ArrowElectronics/10BASE-T1L-MC/Wiki_Page_Images/PCBA_BackView.JPG

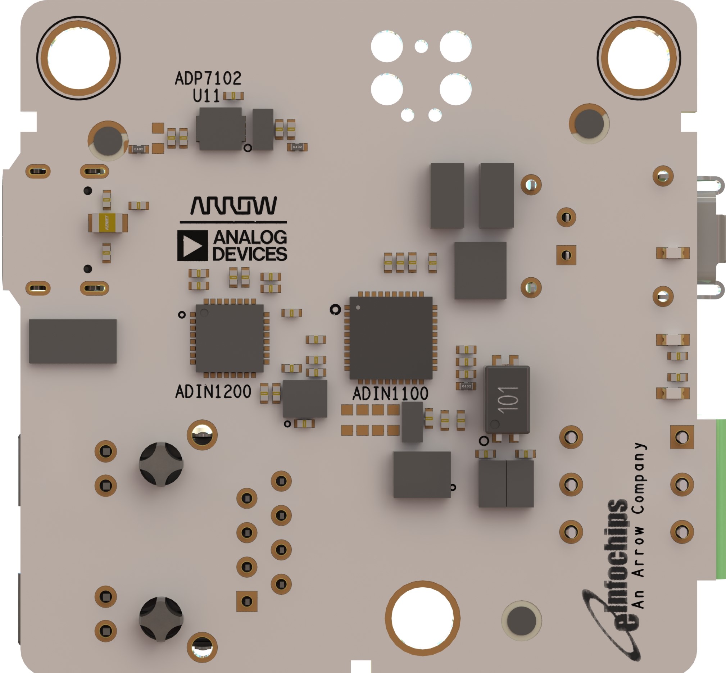
Wiki_Page_Images/PCBA_BackView.JPG
