ArrowElectronics/10BASE-T1L-MC/HW_Package/Gerber/FAB.pdf

D

1

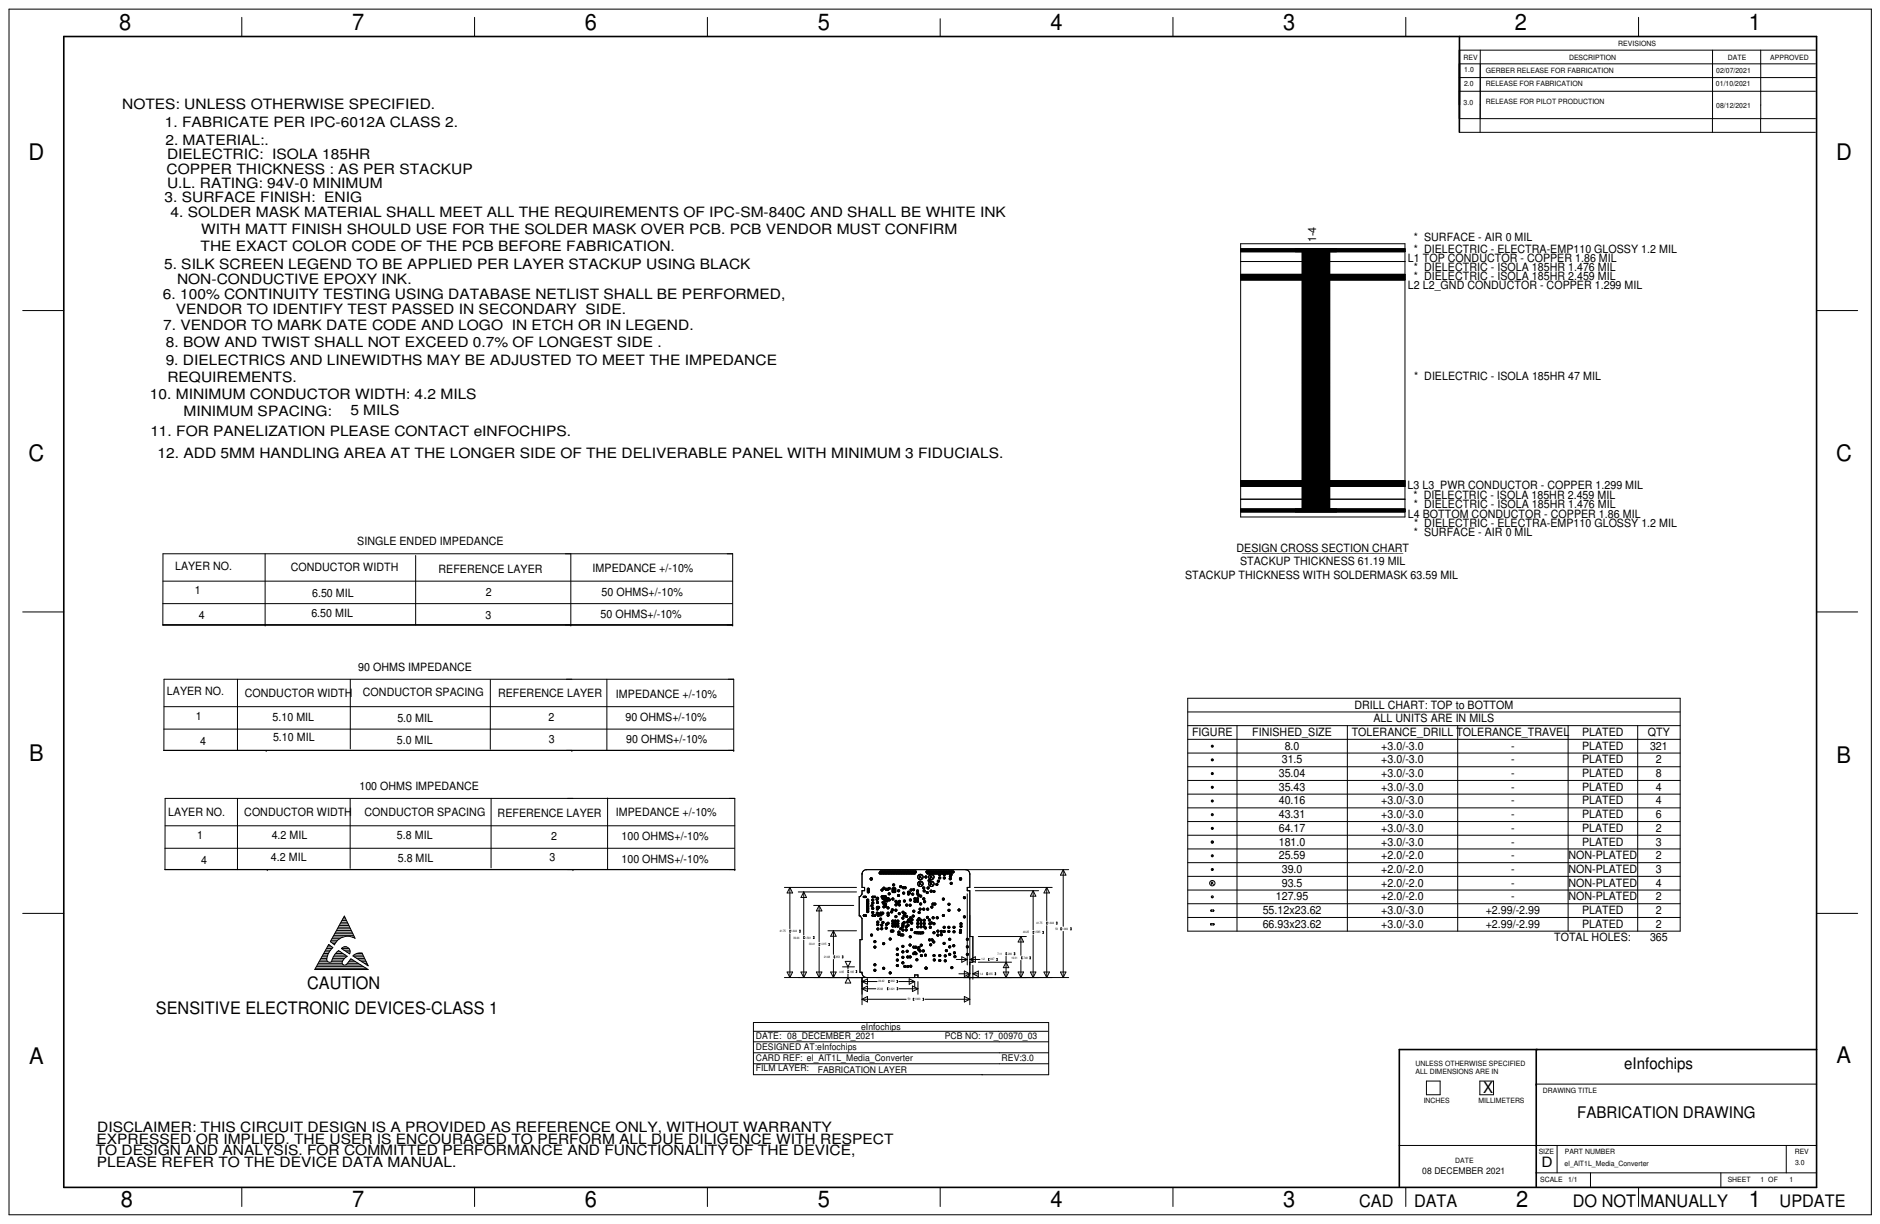
[picture p42: page 1]
REV:3.0; eInfochips; FABRICATION LAYER; PCB NO:; 5.0 MIL; 5.8 MIL; 5.10 MIL; 90 OHMS+/-10%; LAYER NO.; CONDUCTOR WIDTH; 4.2 MIL; el_AlT1L_Media_Converter; REFERENCE LAYER; IMPEDANCE +/-10%; 100 OHMS+/-10%; 90 OHMS IMPEDANCE; 100 OHMS IMPEDANCE; CONDUCTOR SPACING; 08_DECEMBER_2021; PLATED; QTY; FIGURE; TOLERANCE_DRILL FINISHED_SIZE; TOLERANCE_TRAVEL; TOTAL HOLES:; NON-PLATED; CAUTION; MINIMUM SPACING:; 5 MILS; DRAWING TITLE; MILLIMETERS; INCHES; FABRICATION DRAWING; UPDATE; DO NOT MANUALLY; CAD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

REVISIONS

REV | DESCRIPTION | DATE | APPROVED
1.0 | GERBER RELEASE FOR FABRICATION | 02/07/2021

2.0 | RELEASE FOR FABRICATION | 01/10/2021

NOTES: UNLESS OTHERWISE SPECIFIED.

3.0 | | 08/12/2021 RELEASE FOR PILOT PRODUCTION

1. FABRICATE PER IPC-6012A CLASS 2.
2. MATERIAL:.
DIELECTRIC: ISOLA 185HR
COPPER THICKNESS : AS PER STACKUP
U.L. RATING: 94V-0 MINIMUM
3. SURFACE FINISH: ENIG
4. SOLDER MASK MATERIAL SHALL MEET ALL THE REQUIREMENTS OF IPC-SM-840C AND SHALL BE WHITE INK
WITH MATT FINISH SHOULD USE FOR THE SOLDER MASK OVER PCB. PCB VENDOR MUST CONFIRM
THE EXACT COLOR CODE OF THE PCB BEFORE FABRICATION.
5. SILK SCREEN LEGEND TO BE APPLIED PER LAYER STACKUP USING BLACK
NON-CONDUCTIVE EPOXY INK.
6. 100% CONTINUITY TESTING USING DATABASE NETLIST SHALL BE PERFORMED,
VENDOR TO IDENTIFY TEST PASSED IN SECONDARY SIDE.
7. VENDOR TO MARK DATE CODE AND LOGO IN ETCH OR IN LEGEND.
8. BOW AND TWIST SHALL NOT EXCEED 0.7% OF LONGEST SIDE .
9. DIELECTRICS AND LINEWIDTHS MAY BE ADJUSTED TO MEET THE IMPEDANCE
REQUIREMENTS.
10. MINIMUM CONDUCTOR WIDTH: 4.2 MILS
11. FOR PANELIZATION PLEASE CONTACT eINFOCHIPS.
12. ADD 5MM HANDLING AREA AT THE LONGER SIDE OF THE DELIVERABLE PANEL WITH MINIMUM 3 FIDUCIALS.

* SURFACE - AIR 0 MIL
* DIELECTRIC - ELECTRA-EMP110 GLOSSY 1.2 MIL
L1 TOP CONDUCTOR - COPPER 1.86 MIL
* DIELECTRIC - ISOLA 185HR 1.476 MIL
* DIELECTRIC - ISOLA 185HR 2.459 MIL
L2 L2_GND CONDUCTOR - COPPER 1.299 MIL

* DIELECTRIC - ISOLA 185HR 47 MIL

L3 L3_PWR CONDUCTOR - COPPER 1.299 MIL * DIELECTRIC - ISOLA 185HR 2.459 MIL
L4 BOTTOM CONDUCTOR - COPPER 1.86 MIL

SINGLE ENDED IMPEDANCE

DESIGN CROSS SECTION CHART ___________________________ STACKUP THICKNESS 61.19 MIL

LAYER NO. | CONDUCTOR WIDTH | REFERENCE LAYER | IMPEDANCE +/-10%

STACKUP THICKNESS WITH SOLDERMASK 63.59 MIL

1 | 6.50 MIL | 2 | 50 OHMS+/-10%

4 | 6.50 MIL | 3 | 50 OHMS+/-10%

LAYER NO. | CONDUCTOR WIDTH | CONDUCTOR SPACING | REFERENCE LAYER | IMPEDANCE +/-10%

1 | 5.10 MIL | 5.0 MIL | 2 | 90 OHMS+/-10%

DRILL CHART: TOP to BOTTOM
ALL UNITS ARE IN MILS

35.04 | +3.0/-3.0 | - | PLATED | 8
35.43 | +3.0/-3.0 | - | PLATED | 4

39.0 | +2.0/-2.0 | - | NON-PLATED | 3
93.5 | +2.0/-2.0 | - | NON-PLATED | 4
127.95 | +2.0/-2.0 | - | NON-PLATED | 2
55.12x23.62 | +3.0/-3.0 | +2.99/-2.99 | PLATED | 2
66.93x23.62 | +3.0/-3.0 | +2.99/-2.99 | PLATED | 2

SENSITIVE ELECTRONIC DEVICES-CLASS 1

DATE:
DESIGNED AT:eInfochips
CARD REF:
FILM LAYER:

UNLESS OTHERWISE SPECIFIED
ALL DIMENSIONS ARE IN

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

DATE 08 DECEMBER 2021 | SIZE D | PART NUMBER el_AlT1L_Media_Converter | REV 3.0

SCALE 1/1 | | SHEET 1 OF 1
