ArrowElectronics/10BASE-T1L-MC/HW_Package/Block Diagram/ADI_Media_Converter_Block_Diagram_Beta.pdf

# 10BASE-T1L Media Converter Dongle Hardware Architecture

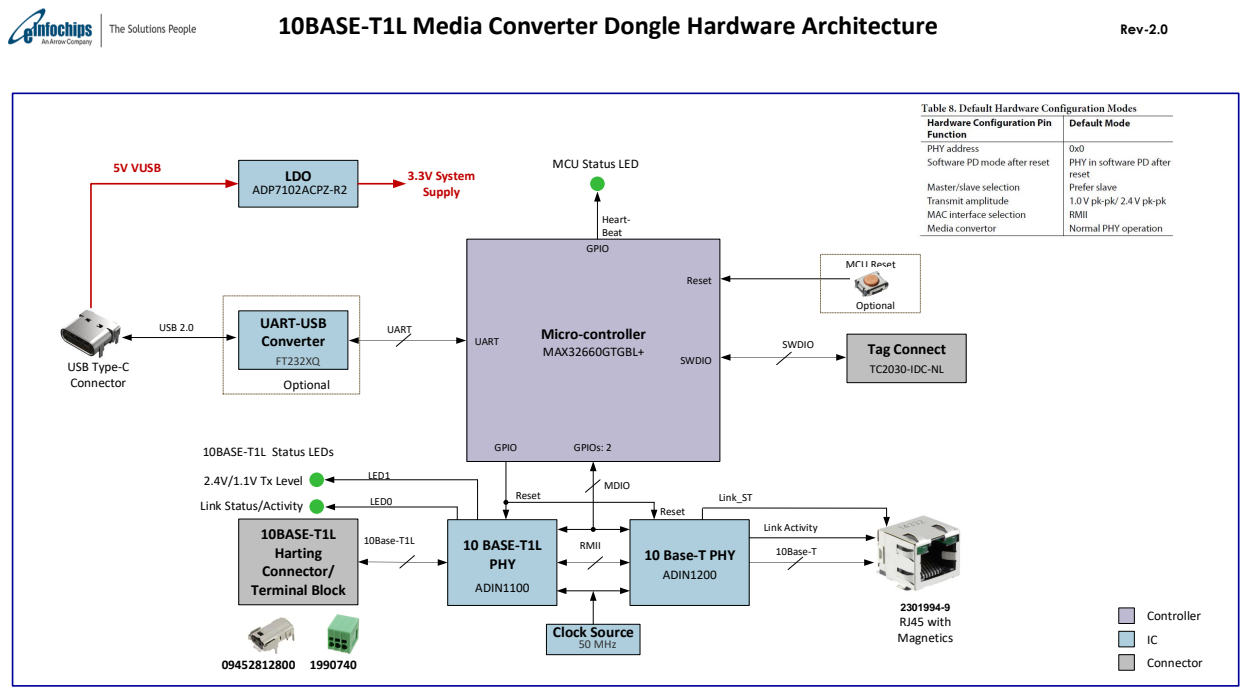
[picture p43: page 1]
10 Base-T PHY; ADIN1200; 10 BASE-T1L PHY; ADIN1100; Micro-controller MAX32660GTGBL+; 2301994-9 RJ45 with Magnetics; 10Base-T; 10BASE-T1L Harting Connector/ Terminal Block; MDIO; 10Base-T1L; RMII; Reset; Clock Source 50 MHz; Rev-2.0; Link_ST; UART; GPIO; GPIOs: 2; Heart- Beat; Link Activity; 10BASE-T1L Status LEDs; Controller; Connector; SWDIO; UART-USB Converter; Optional; USB 2.0; MCU Reset; USB Type-C Connector; LDO ADP7102ACPZ-R2; 3.3V System Supply; 5V VUSB; Tag Connect; TC2030-IDC-NL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

MCU Status LED

2.4V/1.1V Tx Level
Link Status/Activity

# Revision History

Version | Date | Description
0.1 | 1-May-21 | Initial Draft
0.2 | 3-May-21 | Placement Feasibility added
0.3 | 7-May-21 | DC Jack removed
0.4 | 13-May-21 | EEPROM removed; INT and Reset are changed to optional
0.5 | 20-May-21 | Power LED and T1L Link Status LED is removed
0.6 | 28-May-21 | LED1 is added on ADIN1100
0.7 | 02-Jun-21 | Link Status signals to MCU and INT are deleted.
1.0 | 02-Jul-21 | Baselined
1.1 | 2-Sep-21 | RJ45 part# changed to 2301994-9 Buck regulator part# changed to LDO ADP7102ACPZ-R2
2.0 | 07-Oct-21 | Baselined
