ArrowElectronics/10BASE-T1L-MC/HW_Package/Gerber/LAYERS.pdf

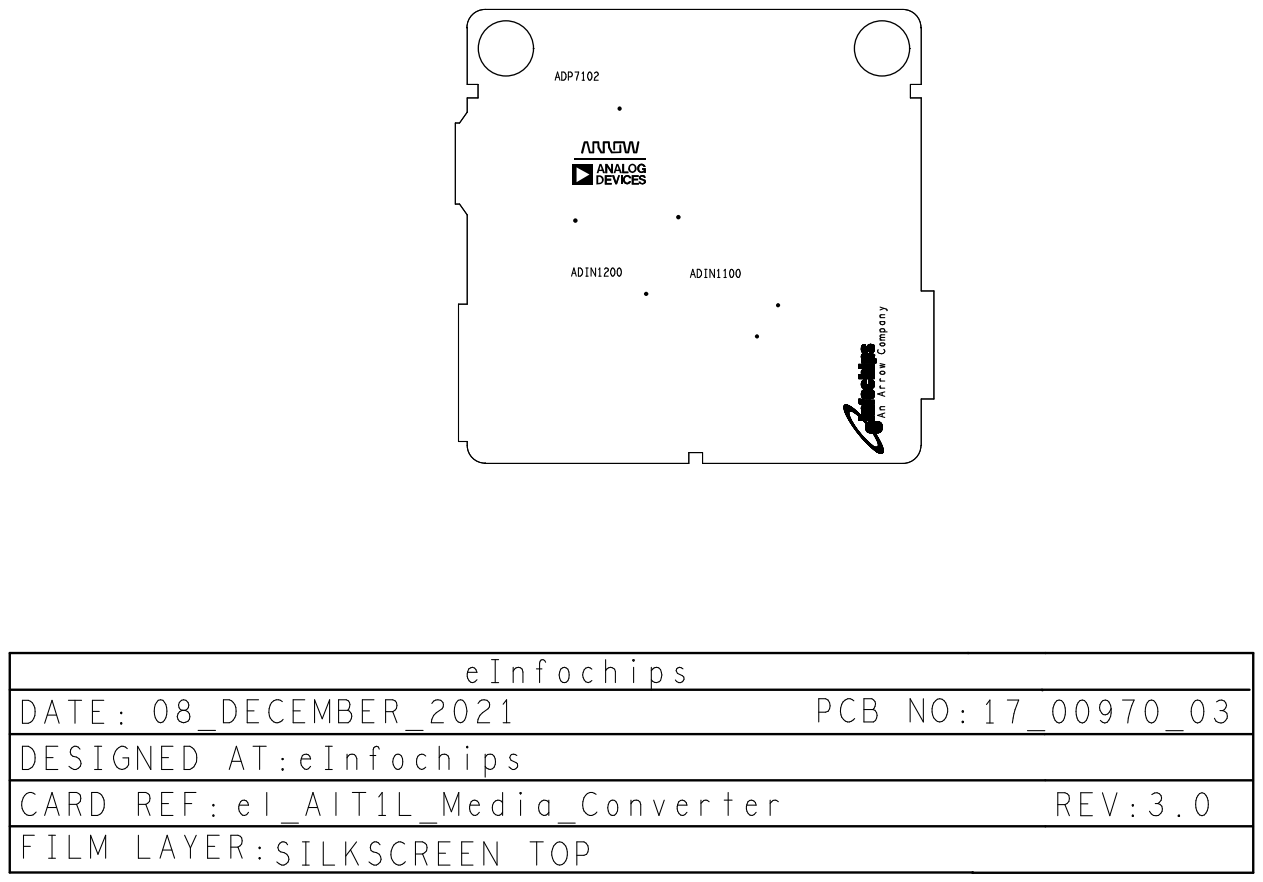
[picture p51: page 1]


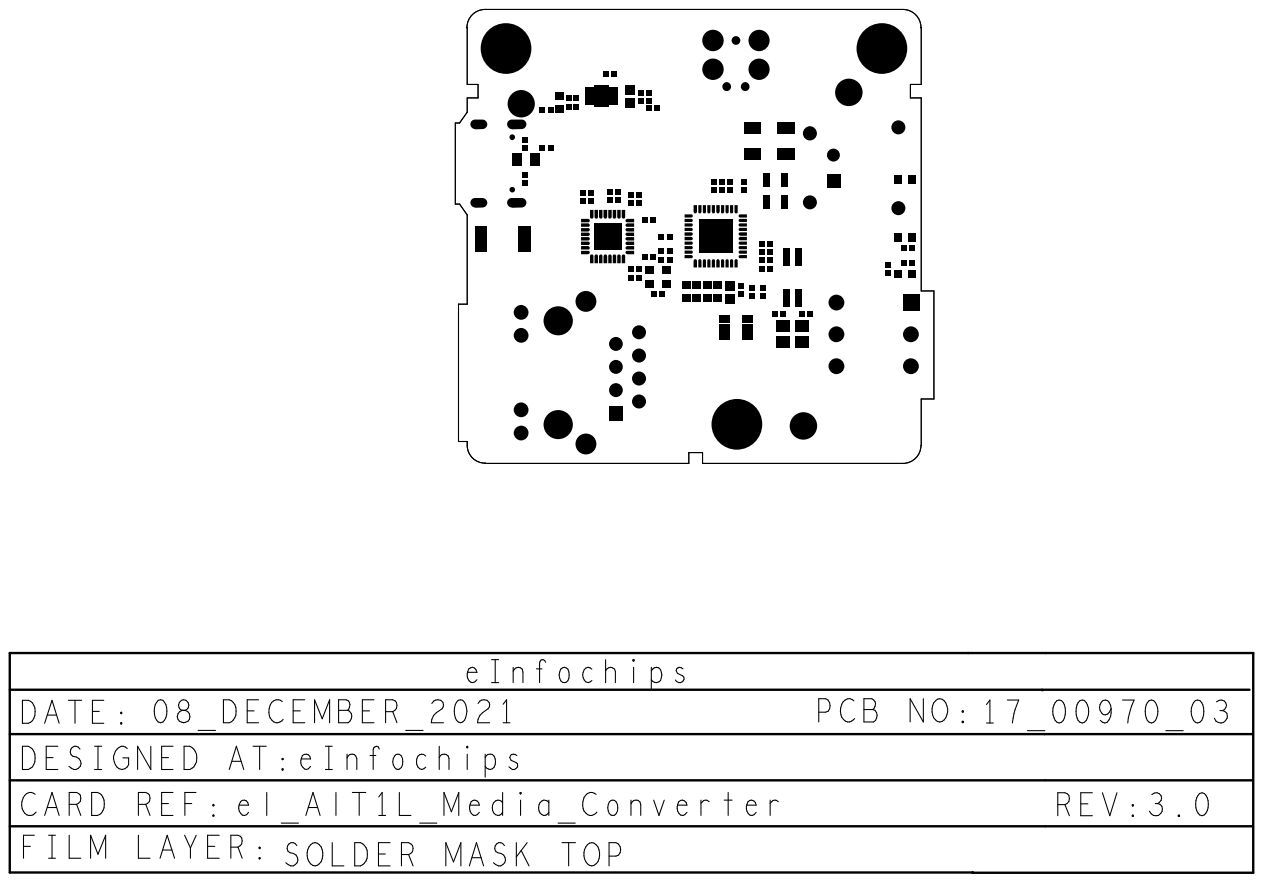
[picture p52: page 3]

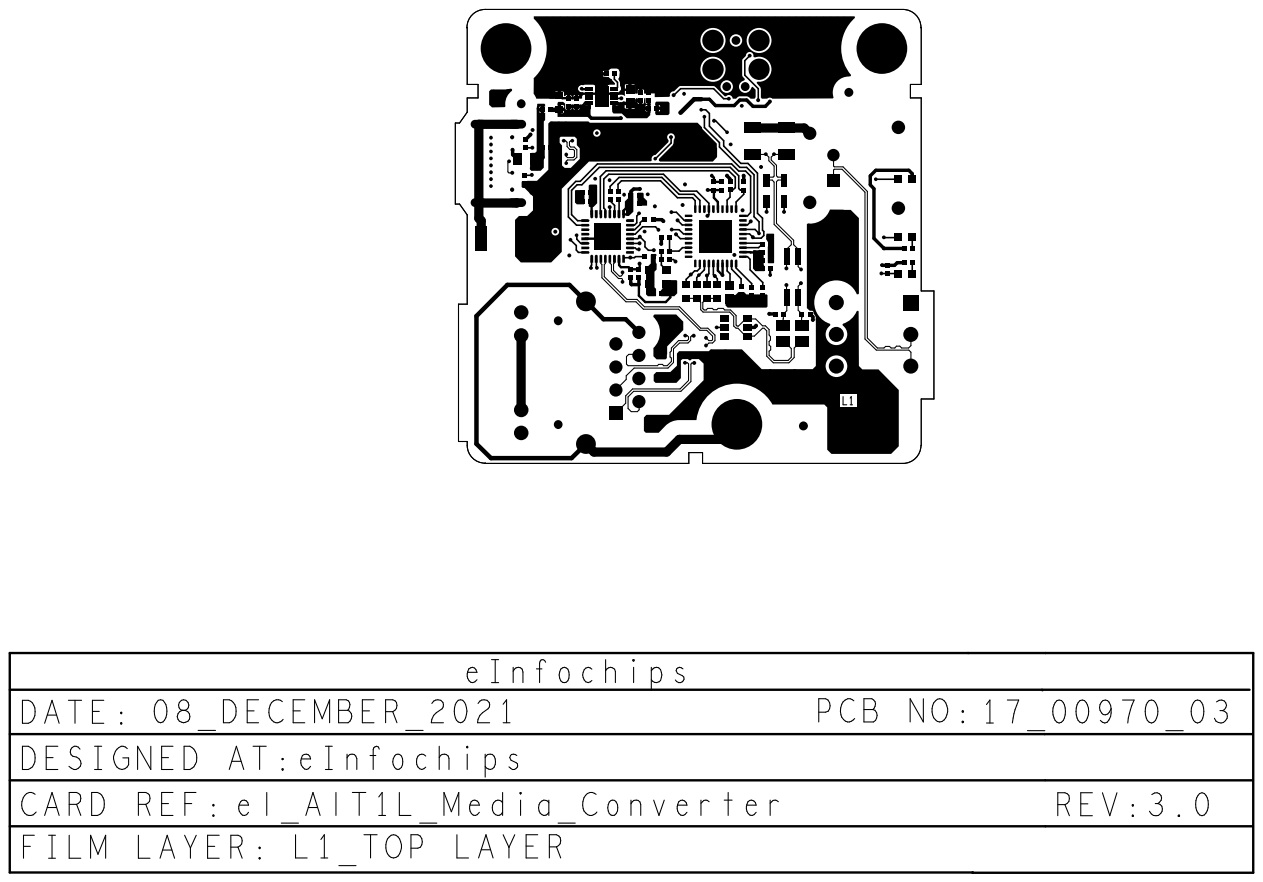
[picture p53: page 4]

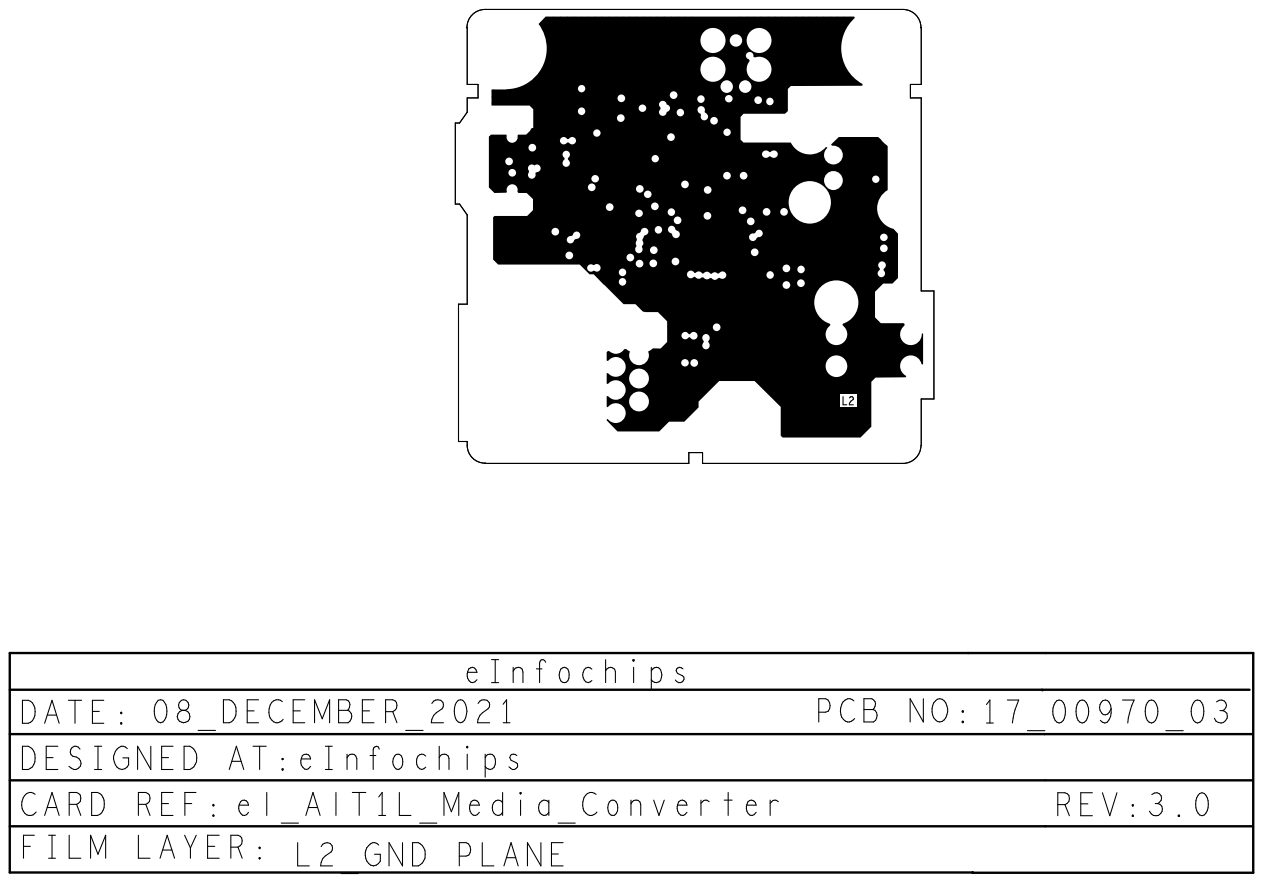
[picture p54: page 5]

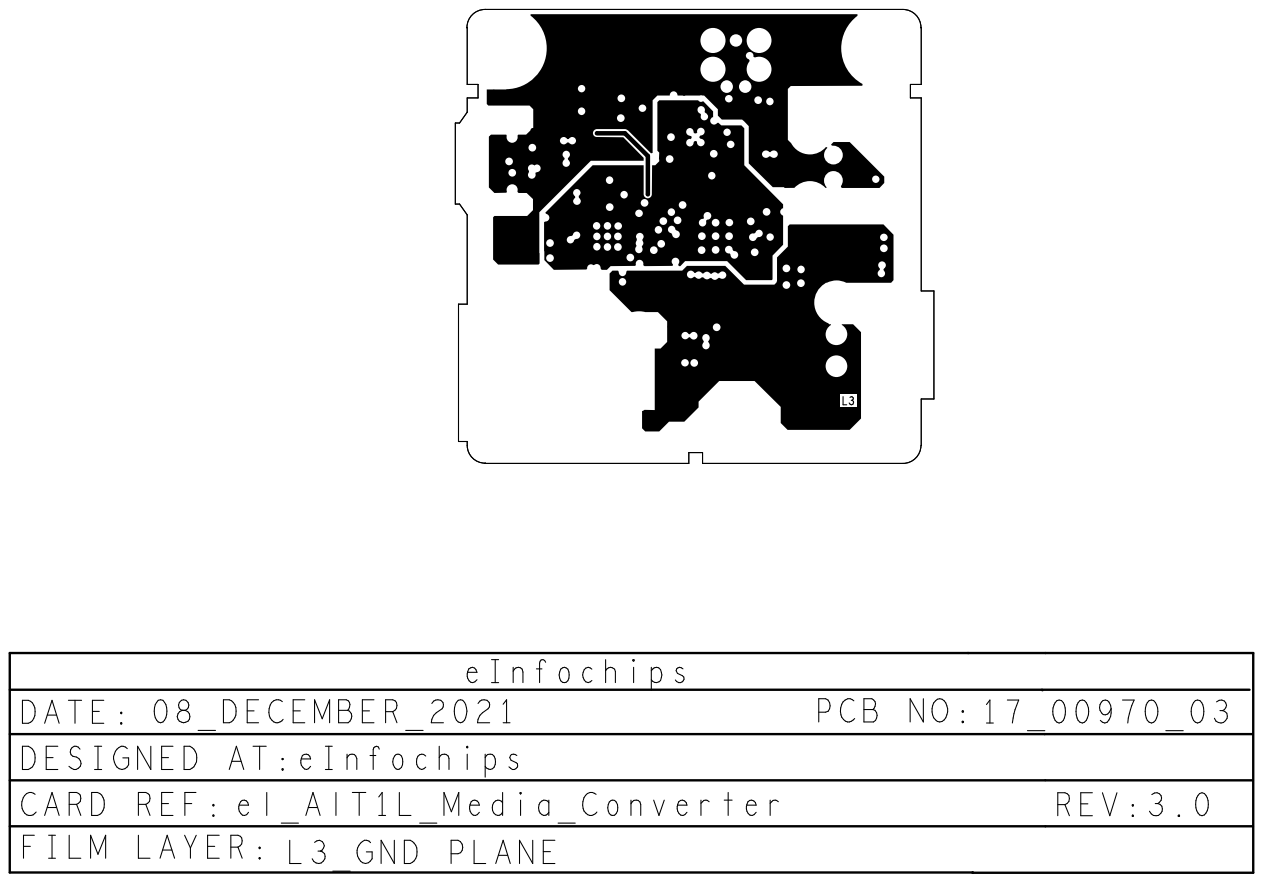
[picture p55: page 6]

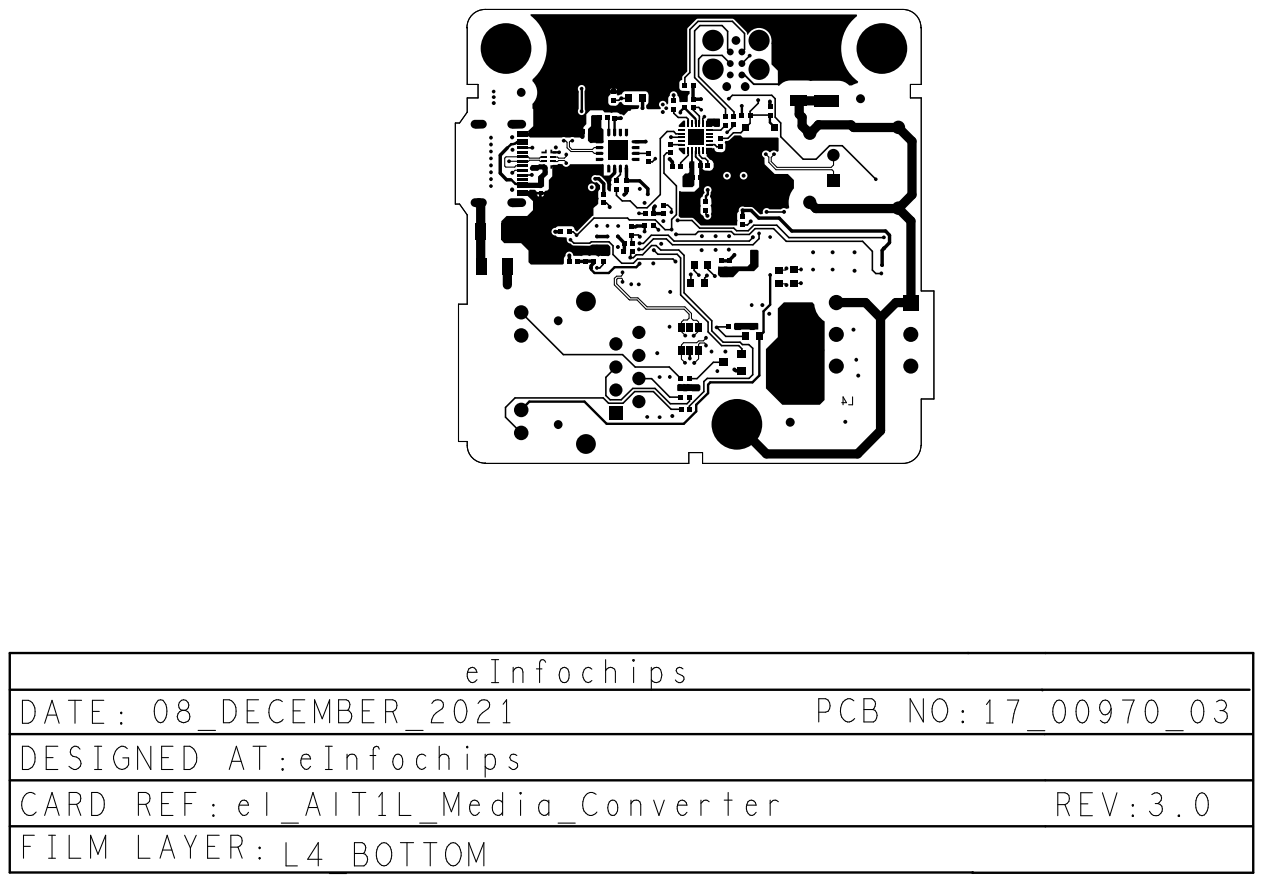
[picture p56: page 7]

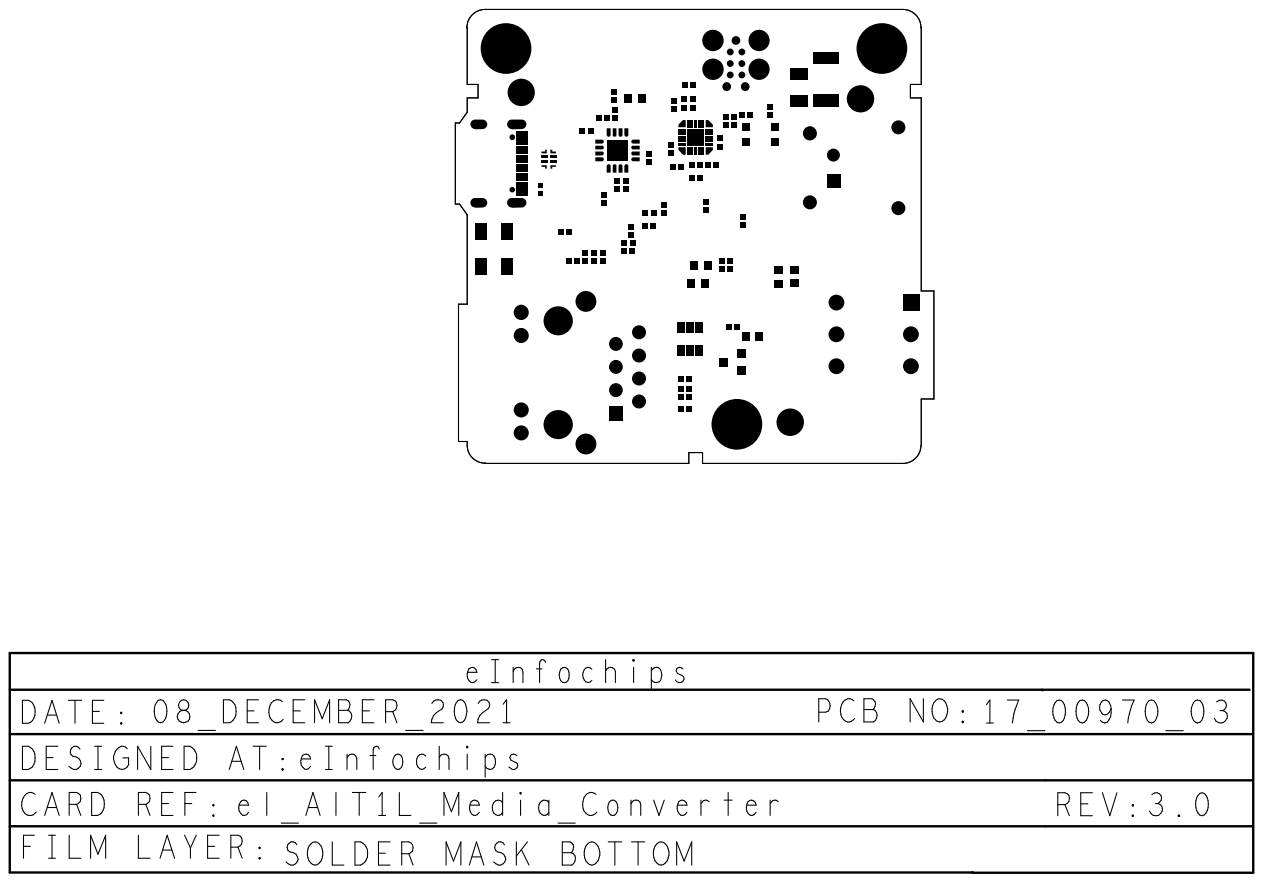
[picture p57: page 8]


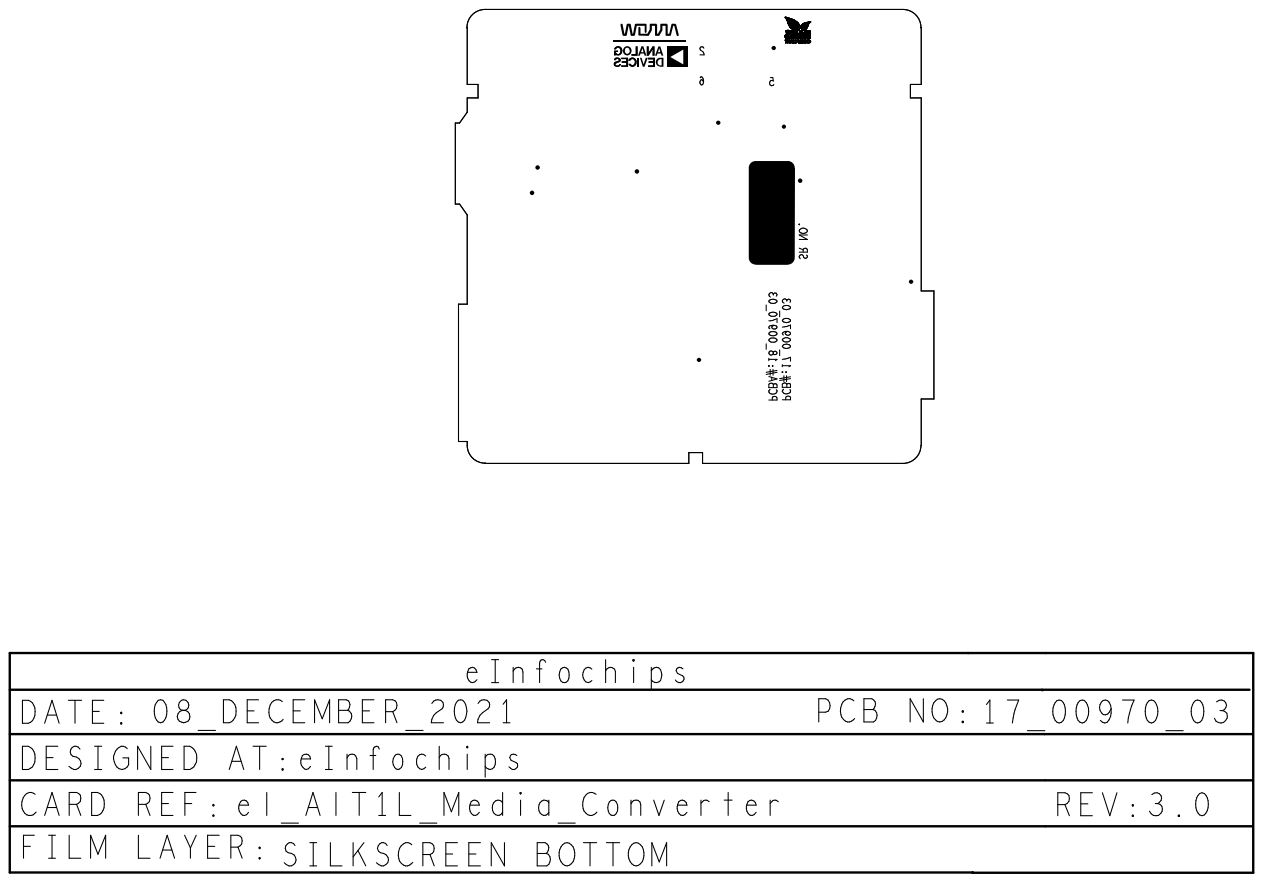
[picture p58: page 10]
